devzendo/easibuildmk2/docs/13-16MHz-scan.png

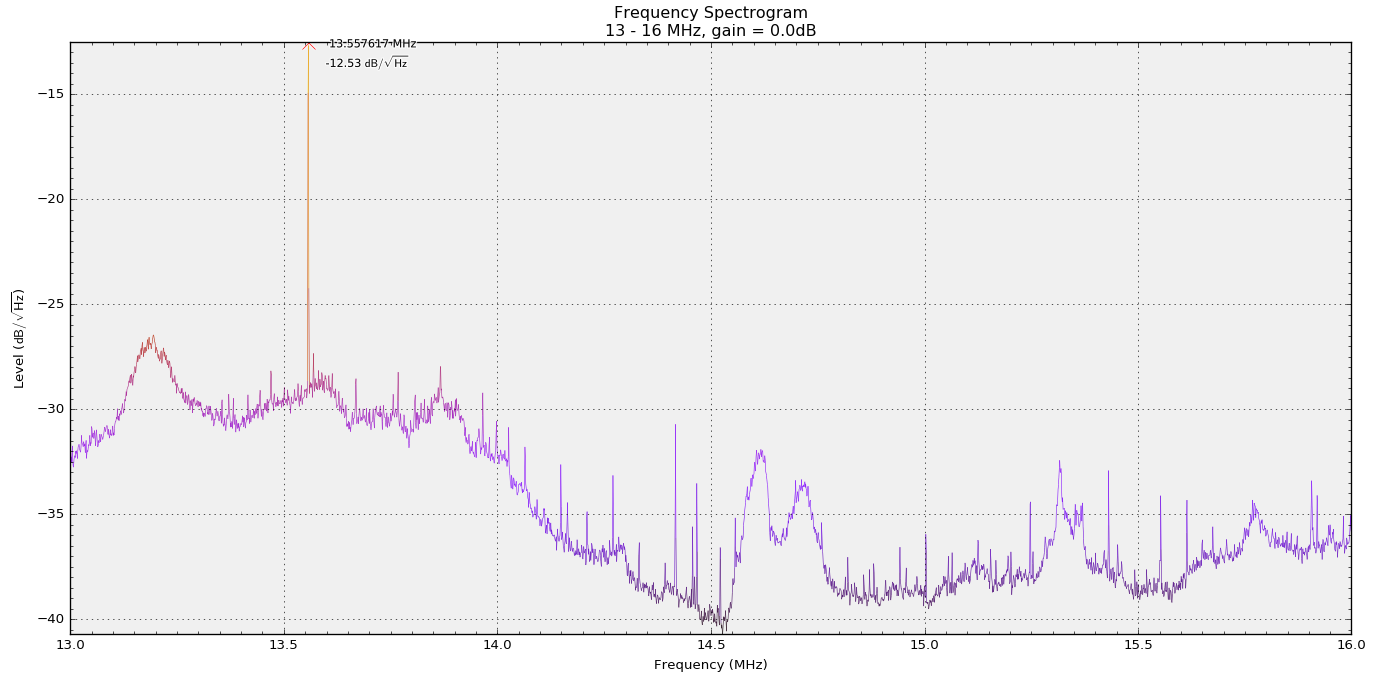
docs/13-16MHz-scan.png
