devzendo/easibuildmk2/docs/control-board.png

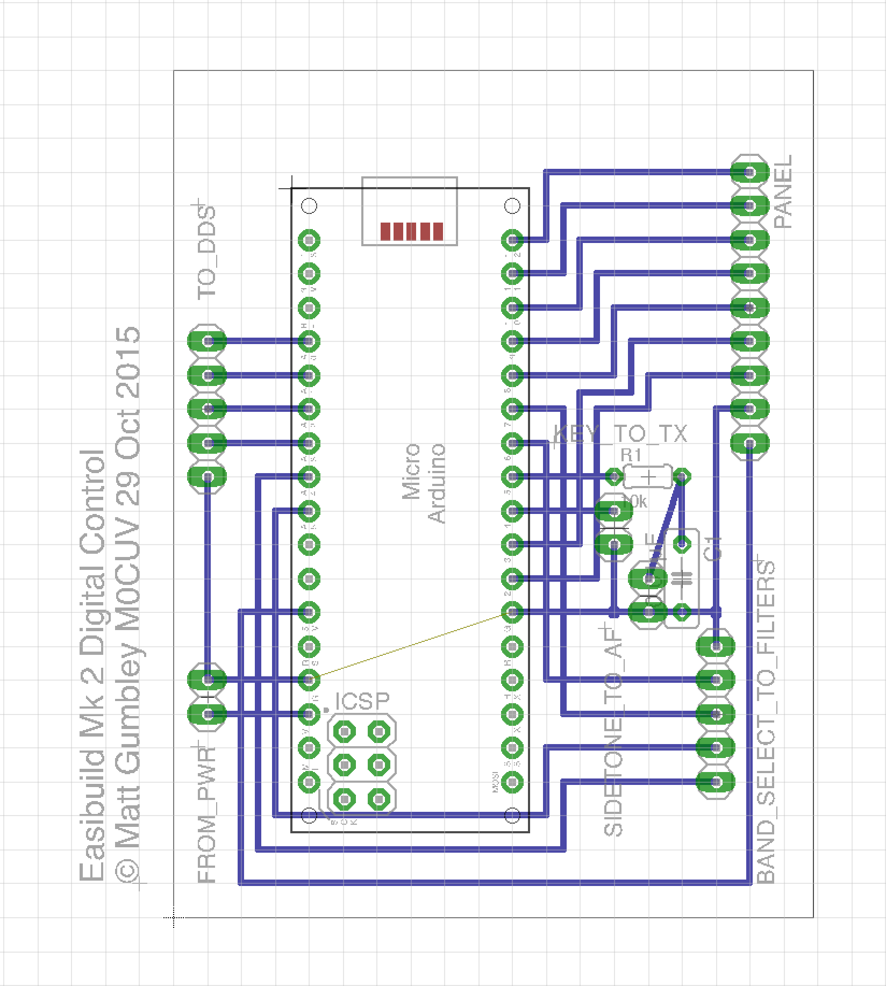
docs/control-board.png
