devzendo/easibuildmk2/docs/control-schematic.png

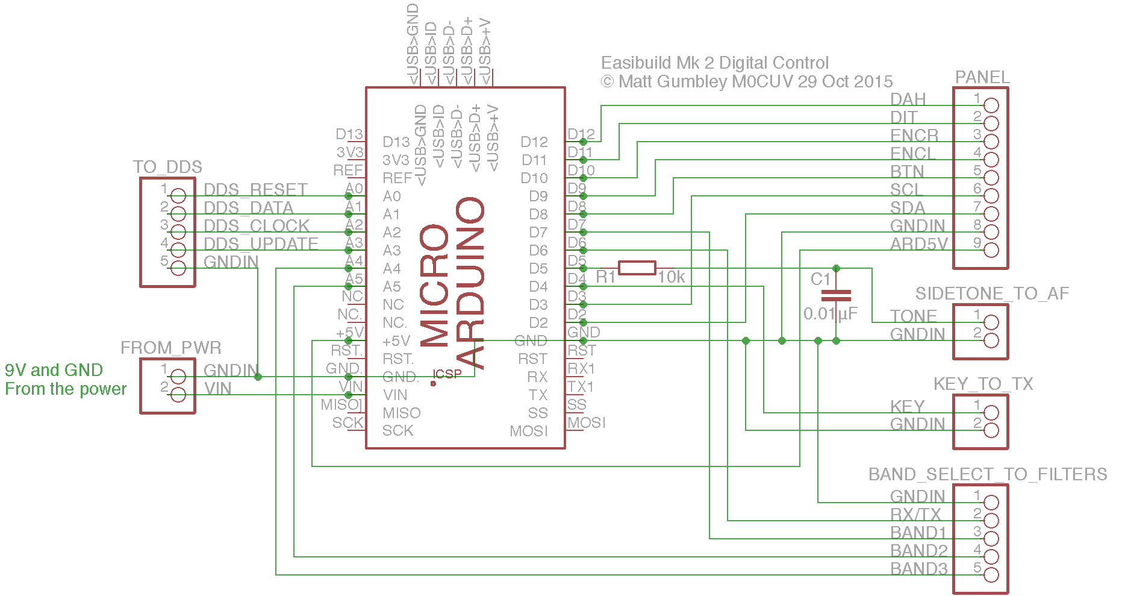
docs/control-schematic.png
