devzendo/easibuildmk2/docs/control-topside-1.jpg

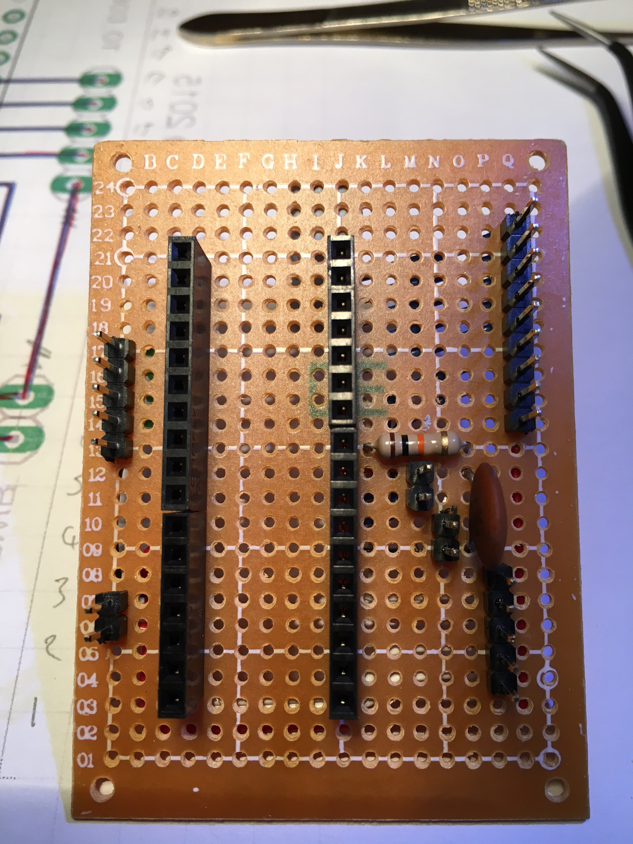
docs/control-topside-1.jpg
