devzendo/easibuildmk2/docs/control-topside-2.jpg

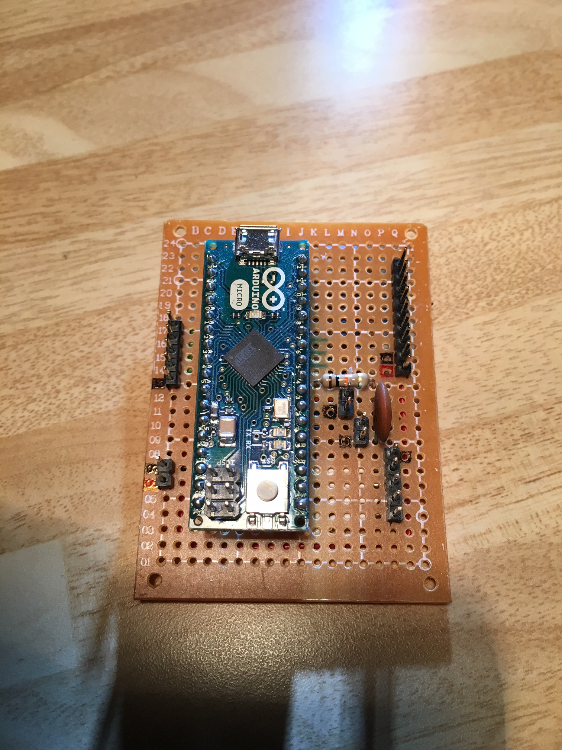
docs/control-topside-2.jpg
