devzendo/easibuildmk2/docs/control-underside-1.jpg

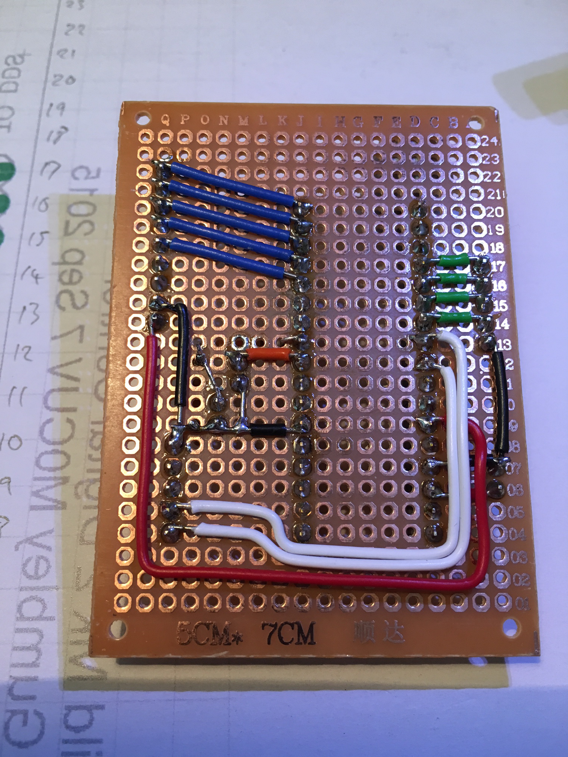
docs/control-underside-1.jpg
