devzendo/easibuildmk2/docs/control-underside-2.jpg

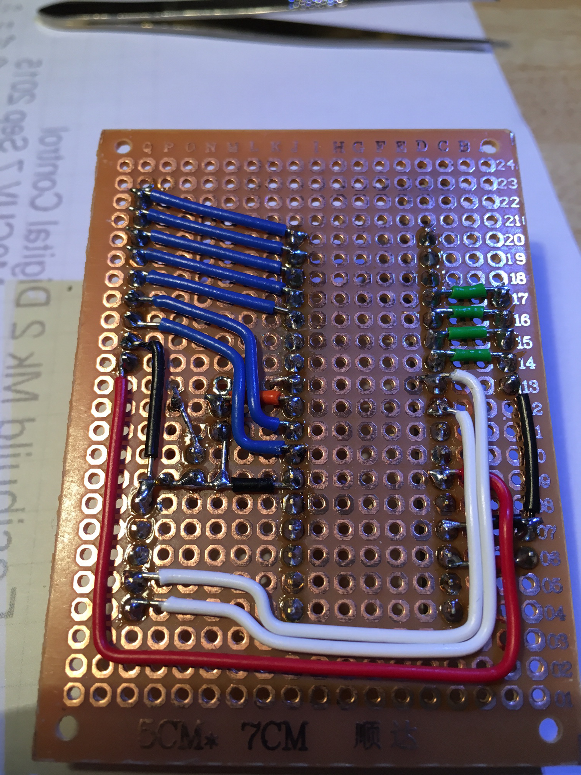
docs/control-underside-2.jpg
