devzendo/easibuildmk2/docs/control-underside-3.jpg

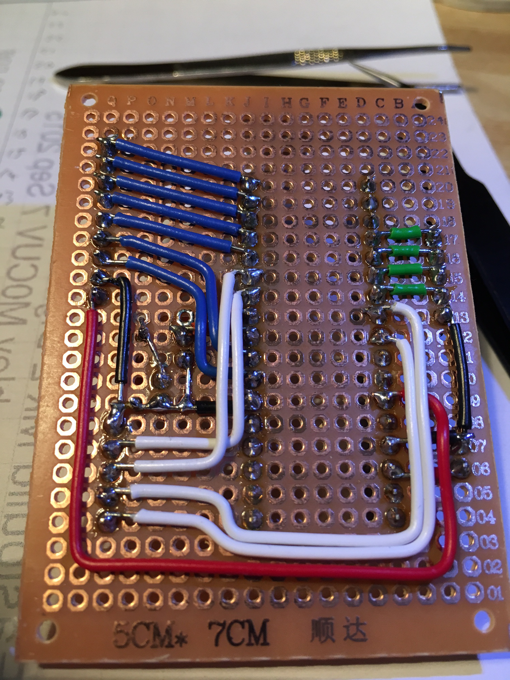
docs/control-underside-3.jpg
