devzendo/easibuildmk2/docs/dds-board.png

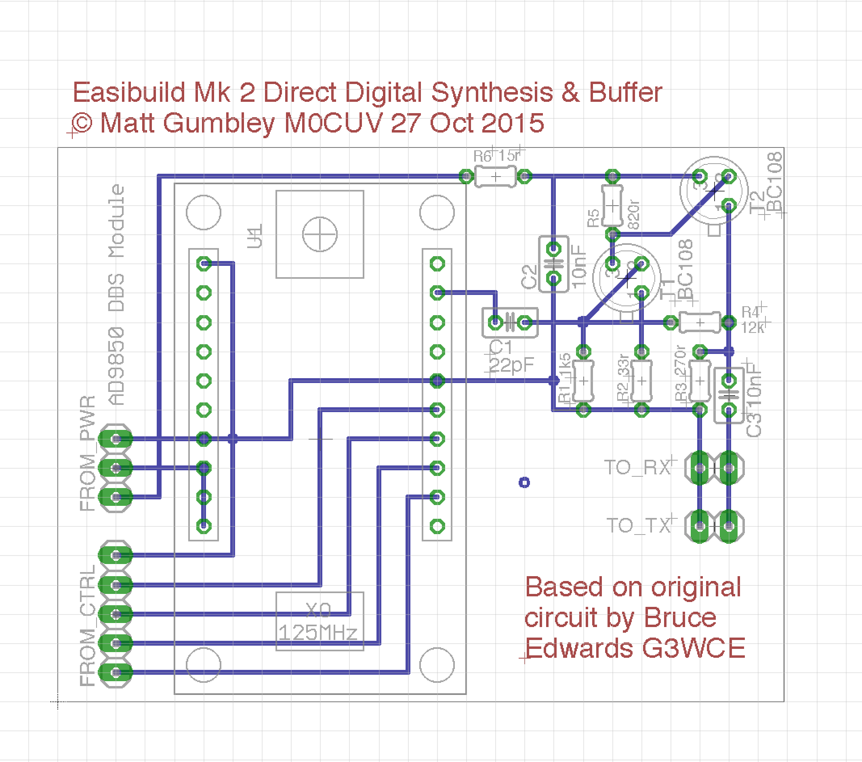
docs/dds-board.png
