devzendo/easibuildmk2/docs/noise-source-board-mirror.png

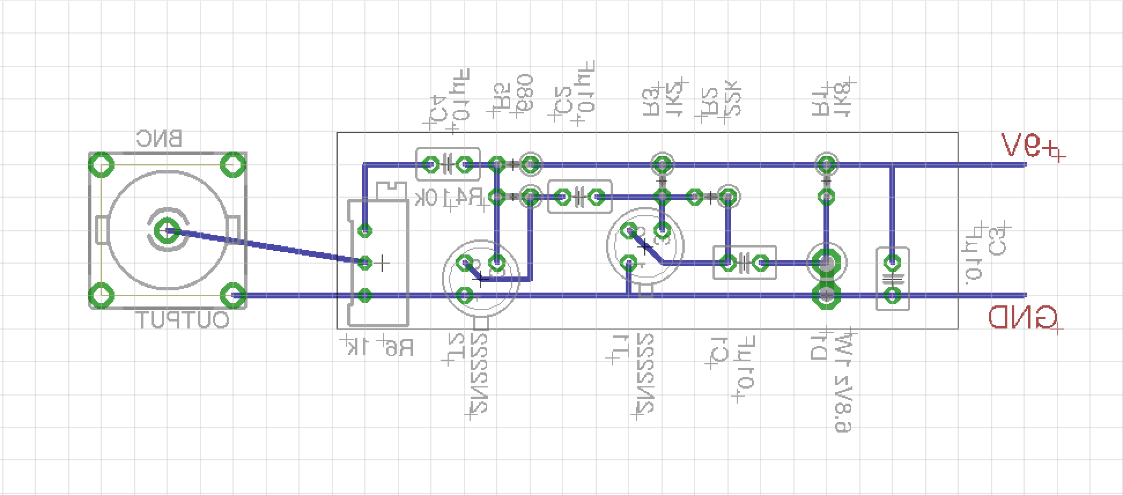
docs/noise-source-board-mirror.png
