devzendo/easibuildmk2/docs/noise-source-board.png

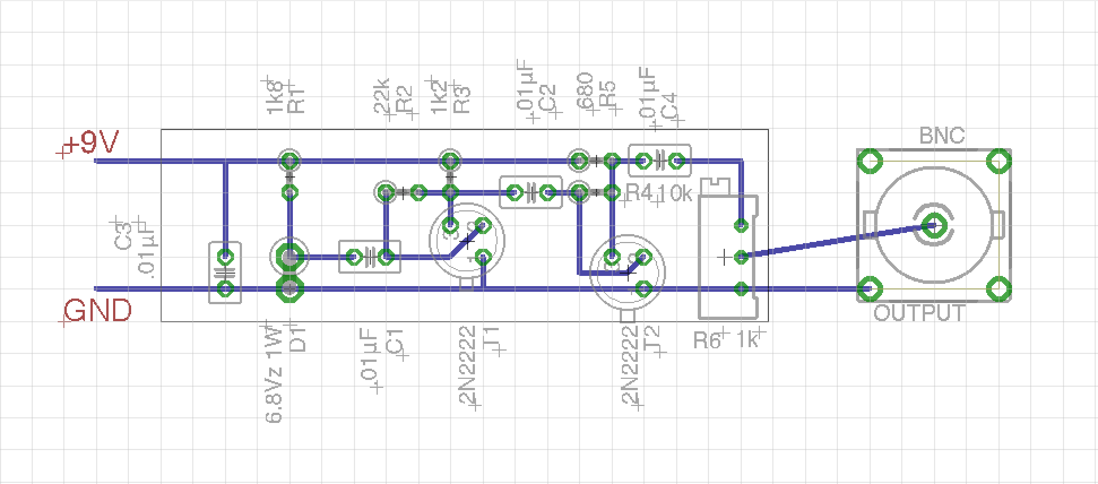
docs/noise-source-board.png
