devzendo/easibuildmk2/docs/noise-source-scope.jpg

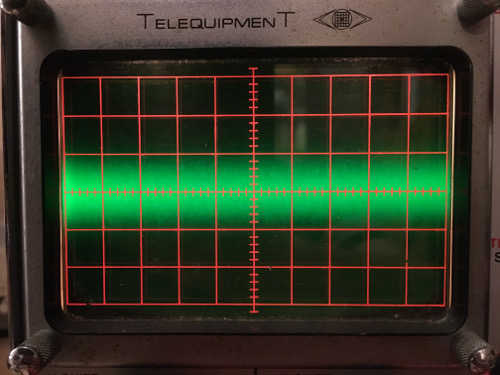
docs/noise-source-scope.jpg
