devzendo/easibuildmk2/docs/noise-vs-dummy-load.png

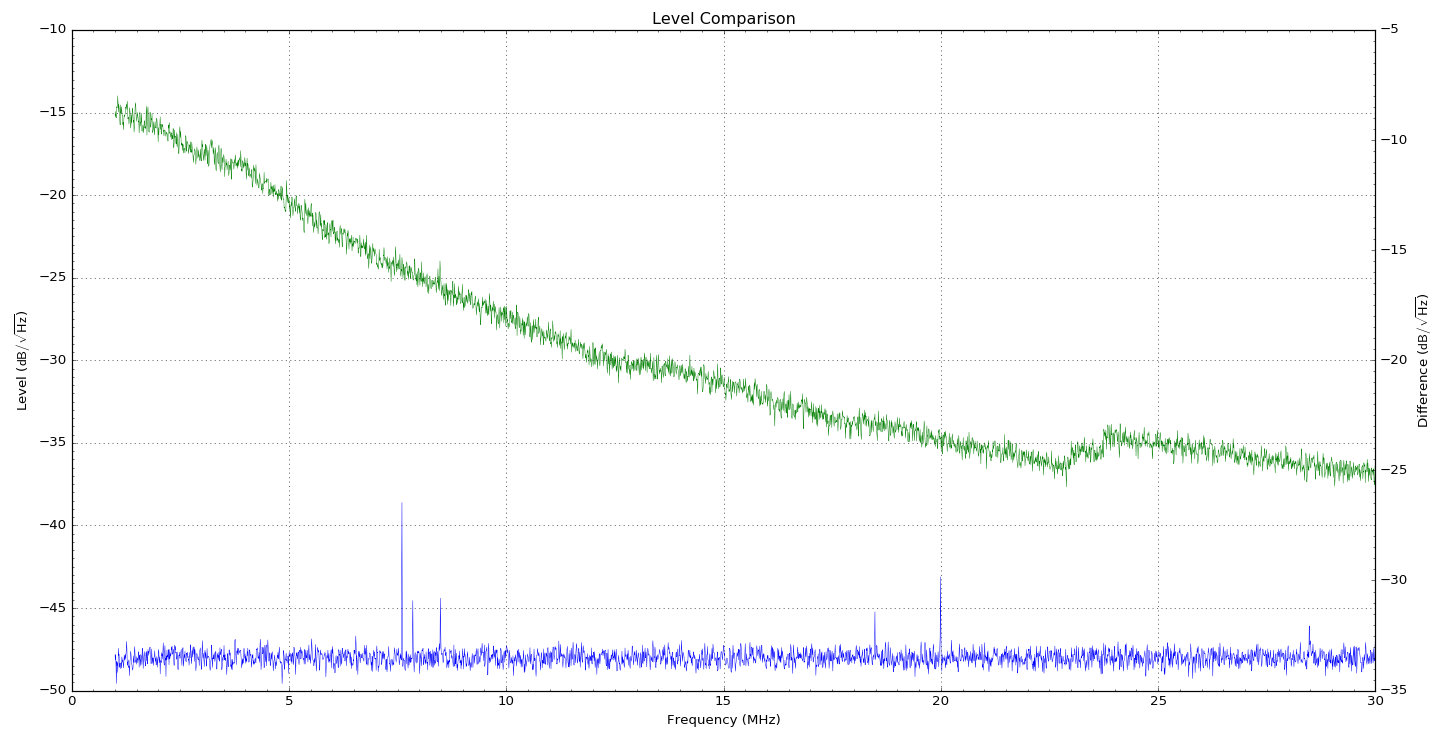
docs/noise-vs-dummy-load.png
