devzendo/easibuildmk2/docs/power-board.png

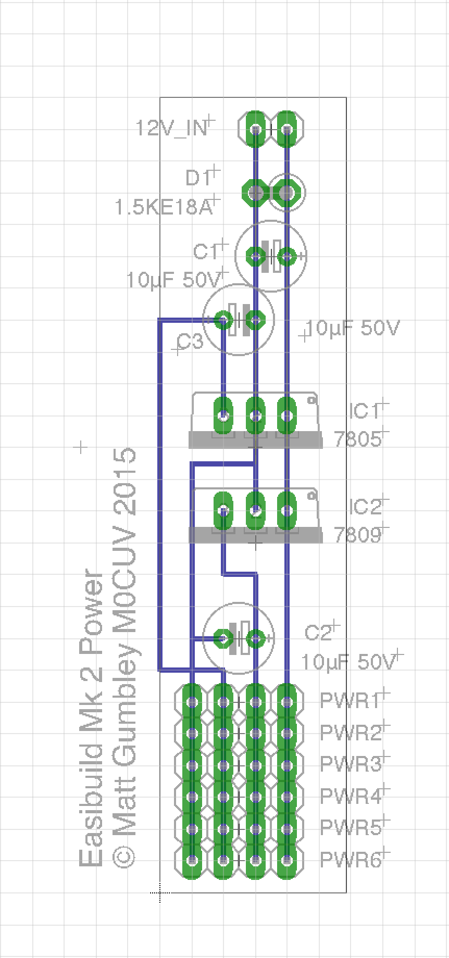
docs/power-board.png
