devzendo/easibuildmk2/docs/power-breadboard.jpg

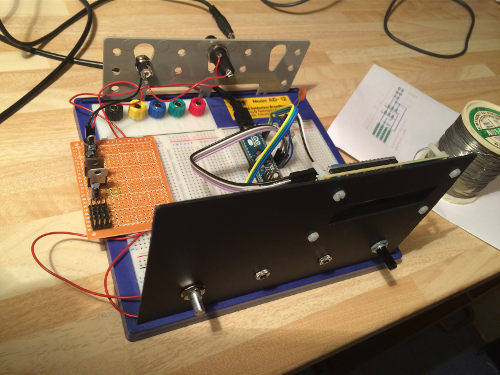
docs/power-breadboard.jpg
