devzendo/easibuildmk2/docs/prototype-board.jpg

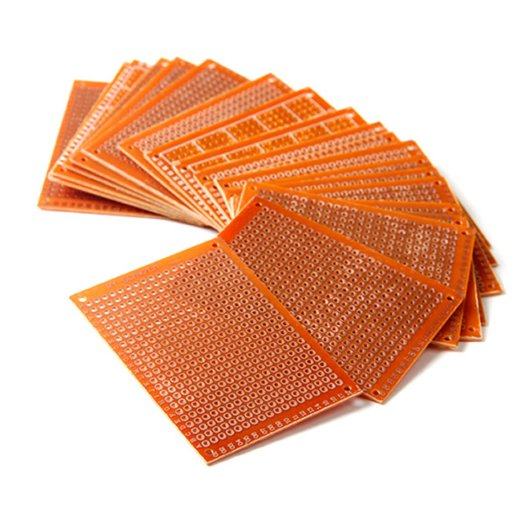
docs/prototype-board.jpg
