devzendo/easibuildmk2/docs/Cauer_DDS_65MHz_7branch.asc

C1: cap; 22p
C2: cap; 33p
C3: cap; 22p
C4: cap; 1p
C5: cap; 22p
C6: cap; 5.6p
C7: cap; 4.7p
L1: ind; .47µ; Rser=.1
L2: ind; .39µ; Rser=.1
L3: ind; .39µ; Rser=.1
R1: res; 200
R2: res; 200
V1: voltage; SINE(0); AC 1.
Named nets: 0
.ac oct 1001 10000000 180000000
