devzendo/easibuildmk2/docs/dds-g3wce.asc

C1: cap; 22p
C2: cap; 10n
C3: cap; 10n
Q1: npn; BC108
Q2: npn; BC108
R1: res; 1k5
R2: res; 33
R3: res; 270
R4: res; 12k
R5: res; 820
R6: res; 15
V1: signal; SINE(0 1 18.096MEG 0 0 0); AC 1.
V2: voltage; 12
Named nets: 0, V, NDDS, NDDSCOUP, BUFMID, BUFOUT, BUFCOUP
.tran 500u
.MODEL BC108 NPN(IS=1.8E-14 ISE=5.0E-14 NF=.9955 NE=1.46
+ BF=400 BR=35.5 IKF=.14 IKR=.03 ISC=1.72E-13 NC=1.27
+ NR=1.005  RB=.56 RE=.6 RC=.25 VAF=80 VAR=12.5 CJE=13E-12
+ CJC=4E-12 VJC=.54 MJC=.33 TF=.64E-9 TR=50.72E-9 mfg=Zetex)
